idpromnut/RFSupply/docs/IMG_20150505_213417.jpg

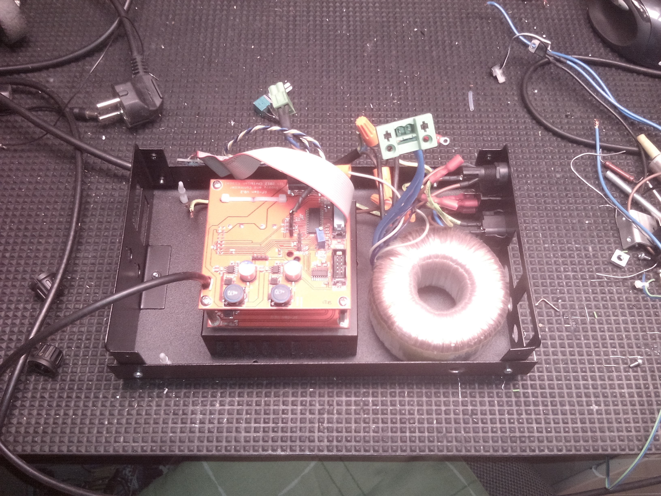
docs/IMG_20150505_213417.jpg
