idpromnut/RFSupply/docs/IMG_20150506_184137.jpg

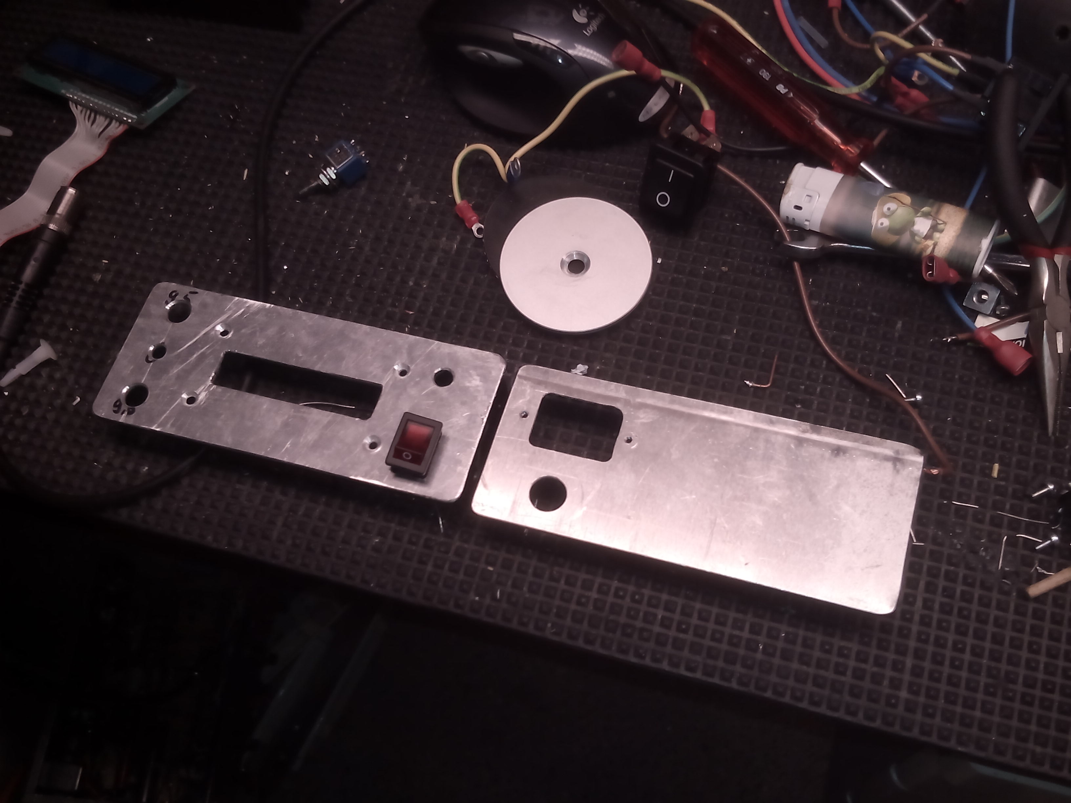
docs/IMG_20150506_184137.jpg
