idpromnut/RFSupply/docs/IMG_20150508_213557.jpg

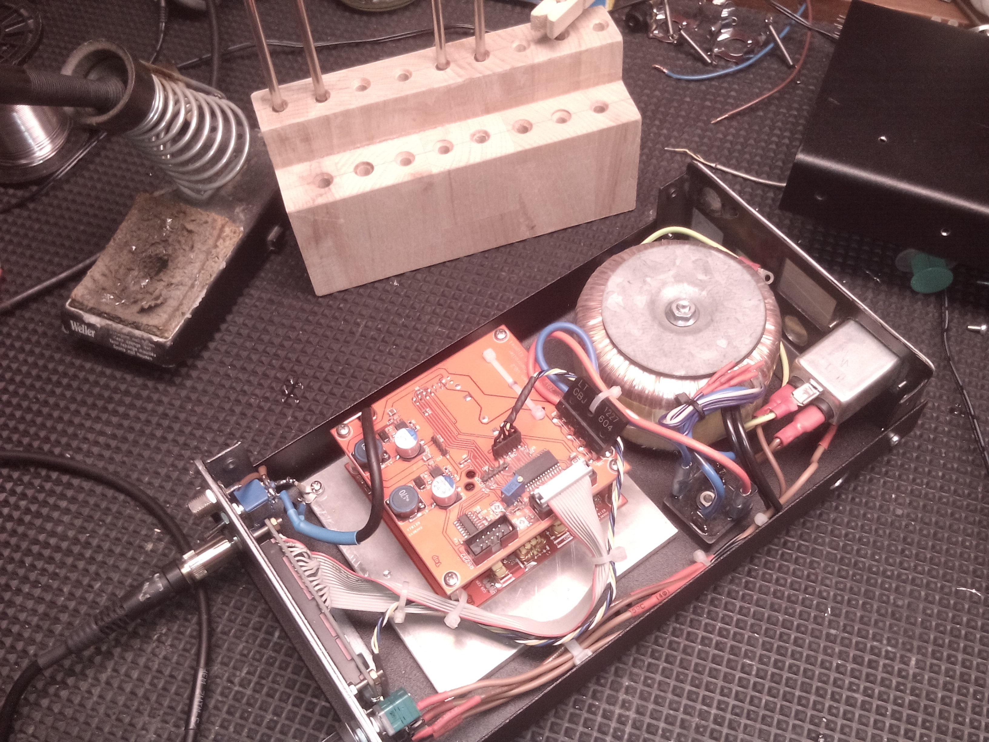
docs/IMG_20150508_213557.jpg
